CaptainDJMax/2526_Maker_LumaDome/06_Documentation/Images/IMG_1706.jpeg

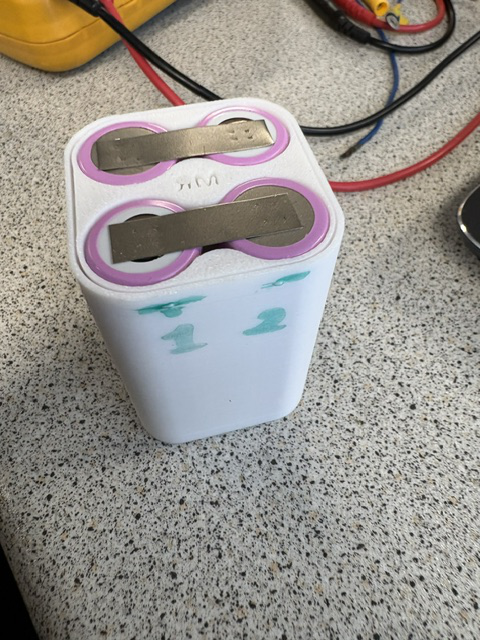
06_Documentation/Images/IMG_1706.jpeg
